Life-lines/OVRTT---Open-VR-Toe-Tracker/Images/arduino_holder_boxCover.jpg

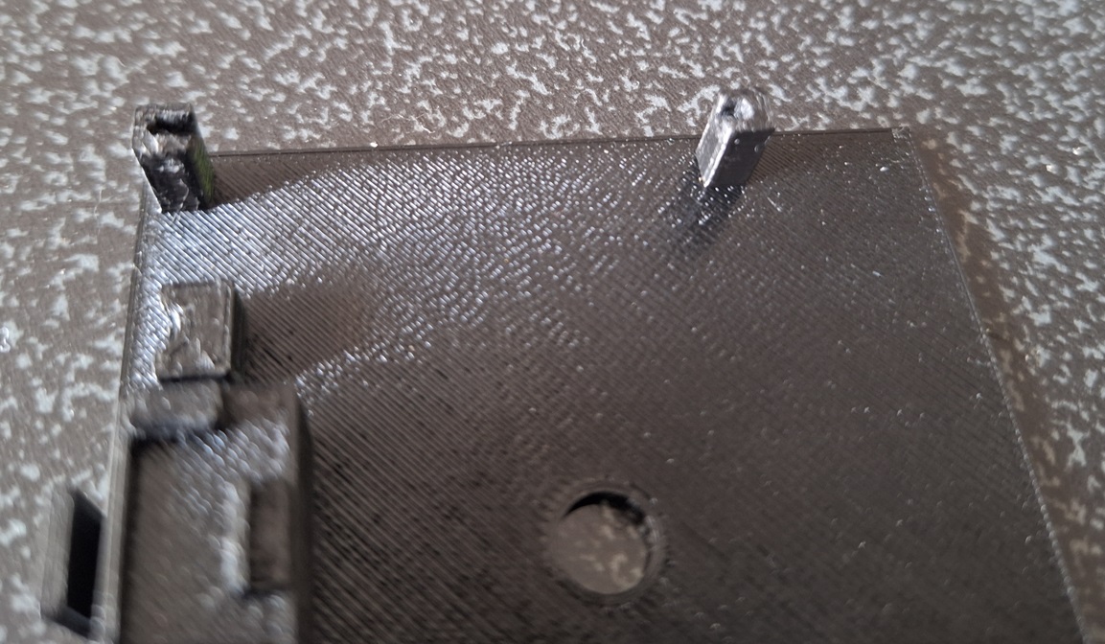
Images/arduino_holder_boxCover.jpg
