Life-lines/OVRTT---Open-VR-Toe-Tracker/Images/sketch_and_config.png

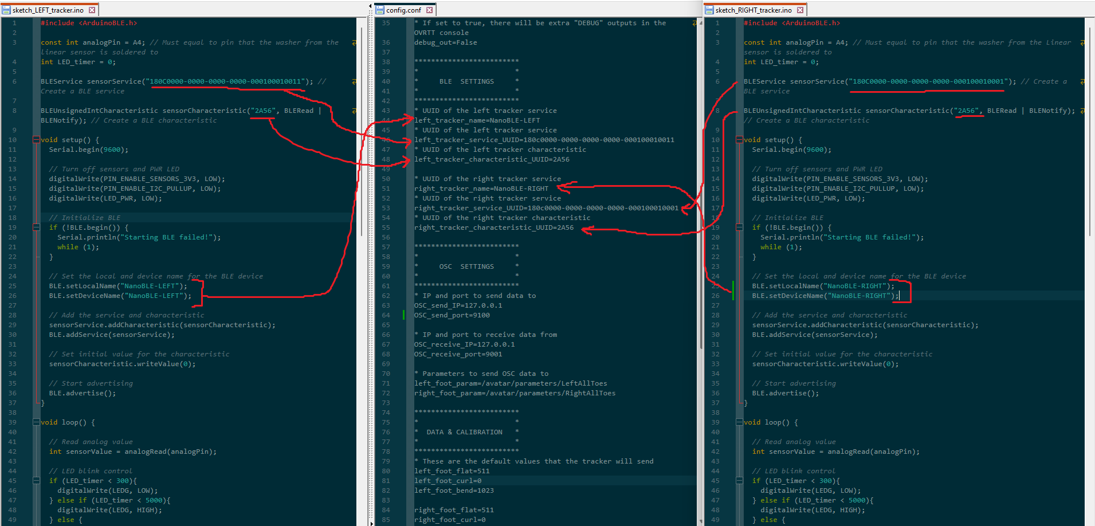
Images/sketch_and_config.png
