Life-lines/OVRTT---Open-VR-Toe-Tracker/Images/string_1.jpg

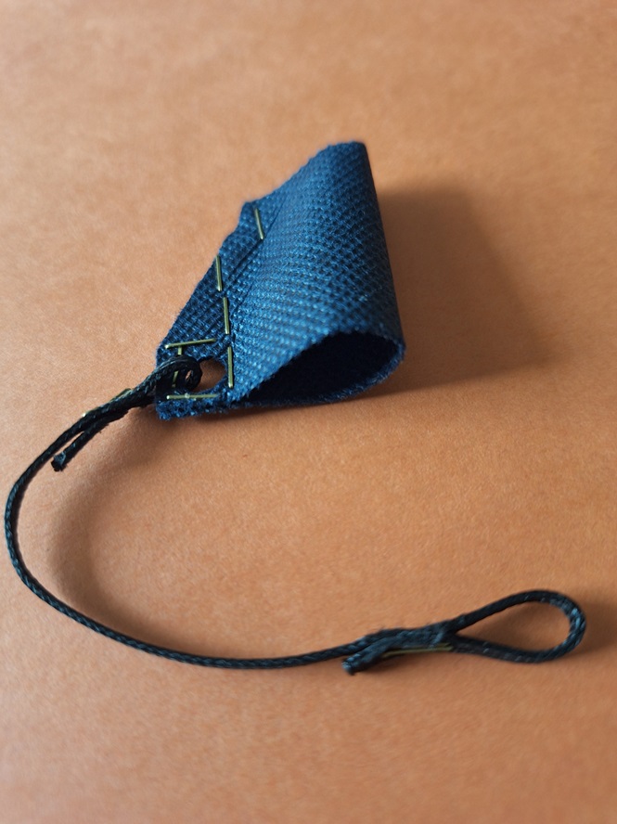
Images/string_1.jpg
