Life-lines/OVRTT---Open-VR-Toe-Tracker/Images/switch_compartment_box.jpg

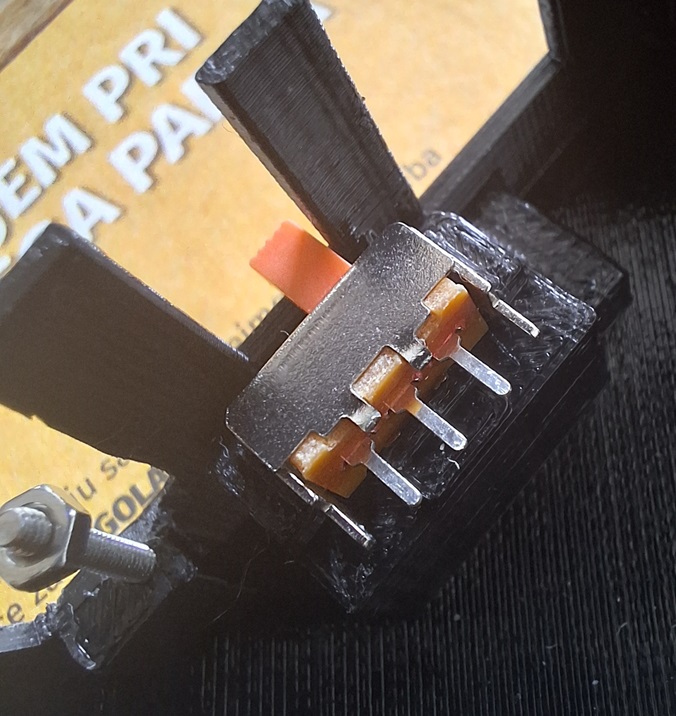
Images/switch_compartment_box.jpg
