Life-lines/OVRTT---Open-VR-Toe-Tracker/Images/switch_compartment_boxCover.jpg

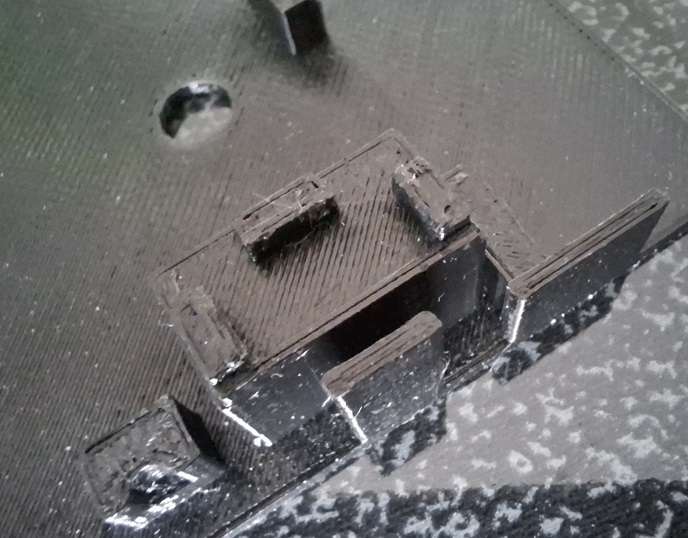
Images/switch_compartment_boxCover.jpg
