Life-lines/OVRTT---Open-VR-Toe-Tracker/Images/assembly_linear_sensor.jpg

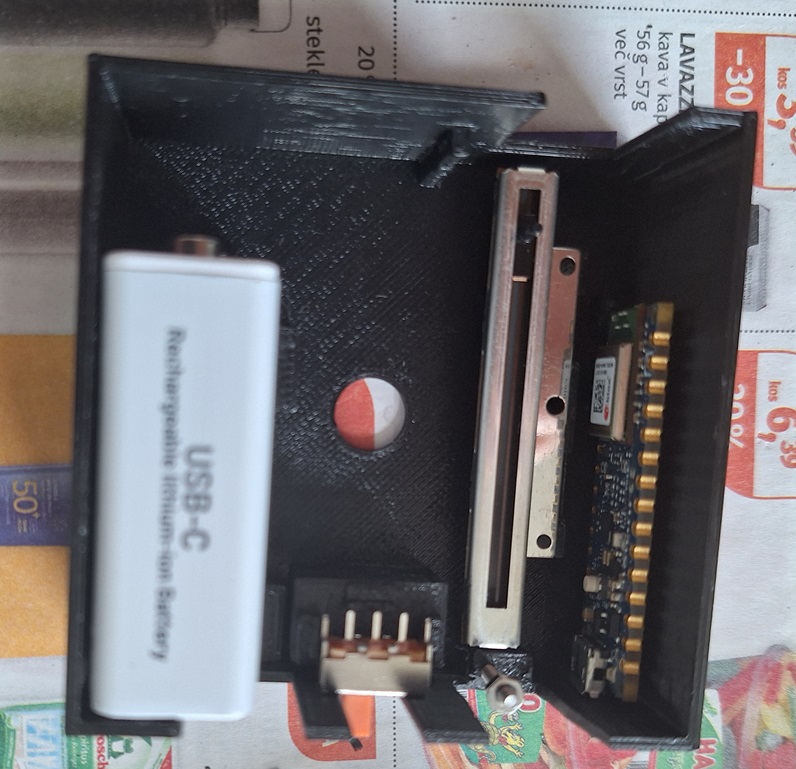
Images/assembly_linear_sensor.jpg
